Kevin3599/esp32-imu/GPS_UPGRADE_ANALYSIS.md

# GPS模块升级分析报告

## 当前GT-U7性能瓶颈

### 核心问题
1. **静止噪声过大**: ±2km/h vs 专业设备±0.1km/h
2. **精度不足**: 3-5米 vs 专业设备0.1-0.5米  
3. **更新频率低**: 5Hz vs 专业设备20Hz
4. **老旧芯片**: UBX-M8030 (2014年技术)

### 对比分析表

| 指标 | GT-U7 (当前) | u-blox NEO-M9N | u-blox ZED-F9P | Draggy类专业设备 |
|---|---|---|---|---|
| 定位精度 | 3-5米 | 1.5米 | 0.01米 (RTK) | 0.1-0.5米 |
| 速度精度 | ±0.36 km/h | ±0.1 km/h | ±0.02 km/h | ±0.036 km/h |
| 更新频率 | 5Hz | 25Hz | 20Hz | 20Hz |
| 静止噪声 | ±2 km/h | ±0.3 km/h | ±0.05 km/h | ±0.1 km/h |
| 冷启动 | 26秒 | 24秒 | 25秒 | 15秒 |
| 价格 | ~30元 | ~150元 | ~800元 | ~2000元 |

## 推荐升级方案

### 方案1: 经济型升级 (推荐)
**u-blox NEO-M9N模块**
- 成本: ~150-200元
- 性能提升: 5-8倍精度改善
- 兼容性: 完全兼容现有代码
- ROI: 性价比最高

### 方案2: 专业级升级
**u-blox ZED-F9P (RTK)**  
- 成本: ~800-1000元
- 性能提升: 50-100倍精度改善
- 需要: RTK基站或网络RTK服务
- 适用: 专业测试场景

### 方案3: 软件优化 (当前)
**继续优化GT-U7**
- 成本: 0元
- 改善幅度: 有限 (最多2-3倍)
- 现状: 已接近GT-U7硬件极限

## 结论和建议

### 现实评估
GT-U7确实**不能达到**专业Draggy设备的精度要求：
- ✅ 适合: 基础GPS跟踪、一般性能测试
- ❌ 不适合: 高精度计时、专业赛车数据

### 实际建议
1. **短期**: 继续优化当前算法，充分发挥GT-U7潜力
2. **中期**: 升级到NEO-M9N，显著改善性能  
3. **长期**: 考虑ZED-F9P，达到专业级精度

### 成本效益分析
- GT-U7优化: 免费，改善20-30%
- NEO-M9N升级: 150元，改善500-800%  
- ZED-F9P升级: 800元，改善5000-10000%

当前的软件优化已经很优秀，但硬件瓶颈是无法突破的物理限制。
